NaokiS28/KSystem-573/Extra Hardware/DDR Amp Cage/GN672-PWB(F) - Stereo Power Amplifier/Images/s-l1600-3.jpg

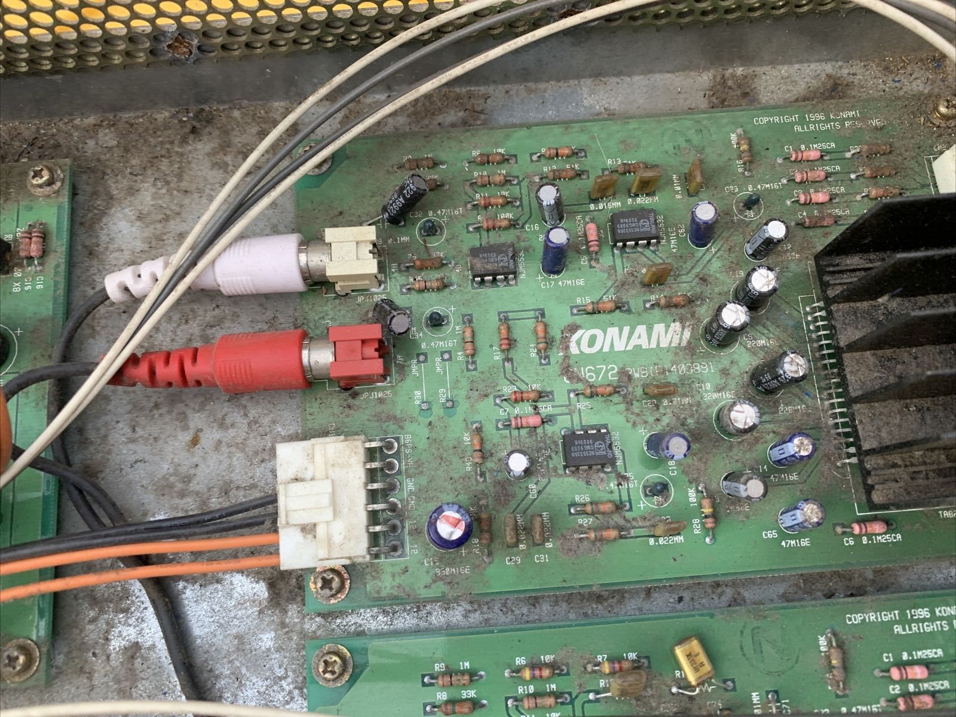
Extra Hardware/DDR Amp Cage/GN672-PWB(F) - Stereo Power Amplifier/Images/s-l1600-3.jpg
