NaokiS28/KSystem-573/Extra Hardware/DDR Amp Cage/GX874-PWB(C) - Stereo pre-amp/images/i-img1200x900-1629526307lxgmrb121866.jpg

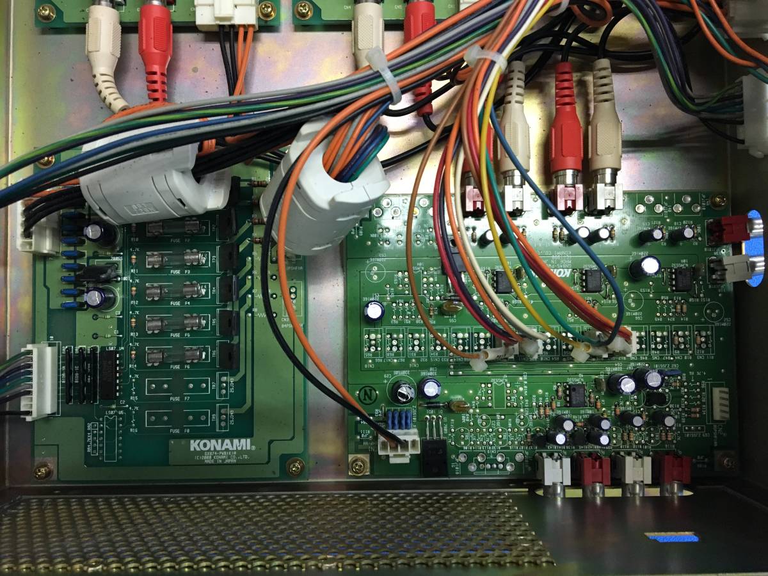
Extra Hardware/DDR Amp Cage/GX874-PWB(C) - Stereo pre-amp/images/i-img1200x900-1629526307lxgmrb121866.jpg
