NaokiS28/KSystem-573/Extra Hardware/DDR Amp Cage/GX874-PWB(C) - Stereo pre-amp/images/s-l1600-4.jpg

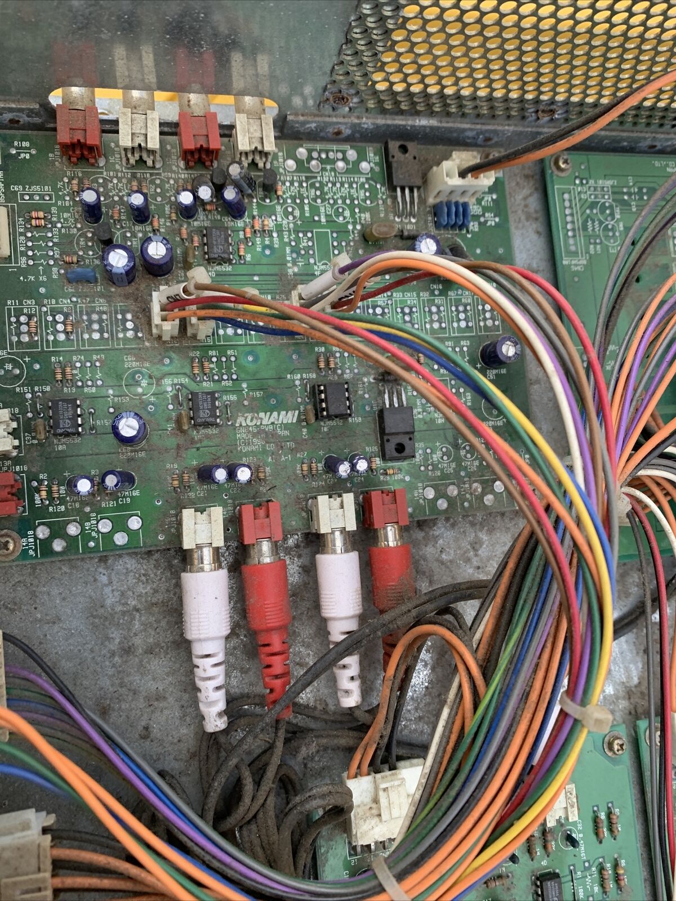
Extra Hardware/DDR Amp Cage/GX874-PWB(C) - Stereo pre-amp/images/s-l1600-4.jpg
