NaokiS28/KSystem-573/Extra Hardware/DDR Amp Cage/Images/IMG_0117.jpg

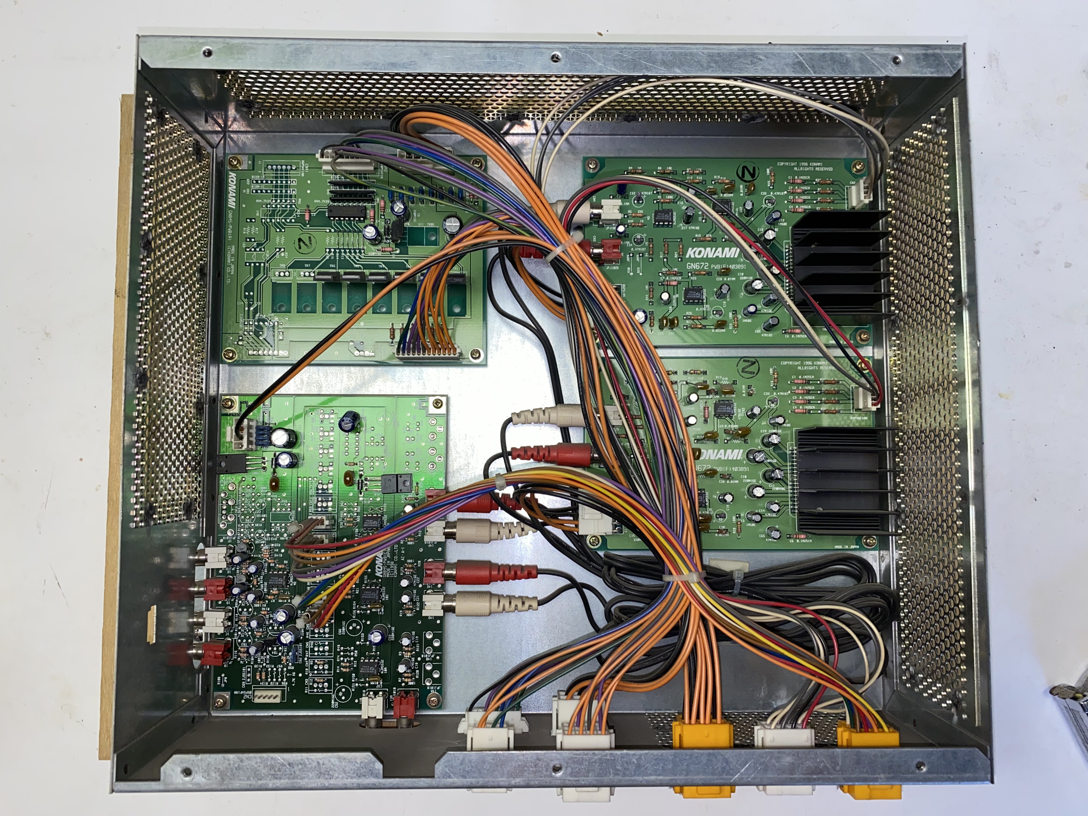
Extra Hardware/DDR Amp Cage/Images/IMG_0117.jpg
