NaokiS28/KSystem-573/Extra Hardware/DDR Amp Cage/Images/s-l1600.jpg

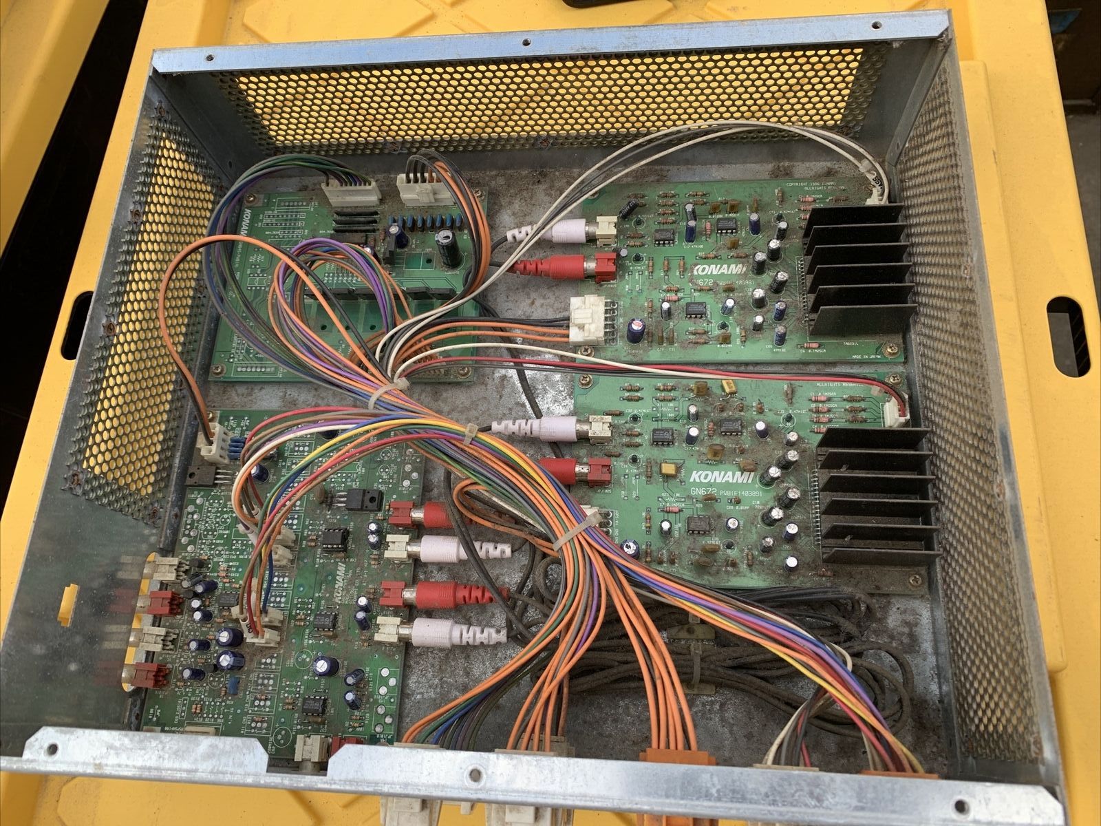
Extra Hardware/DDR Amp Cage/Images/s-l1600.jpg
