NaokiS28/KSystem-573/Extra Hardware/Expansion Boards/GE765-PWB(B)A/E765B1 PAL/E765B1-PAL.png

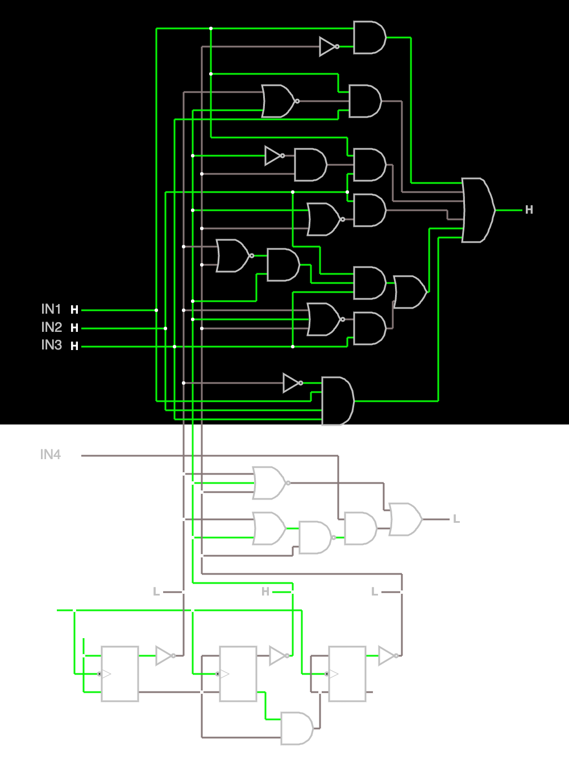
Extra Hardware/Expansion Boards/GE765-PWB(B)A/E765B1 PAL/E765B1-PAL.png
