NaokiS28/KSystem-573/Extra Hardware/Expansion Boards/GunMania IO (PWB0000073070)/Images/s-l1600-1.jpg

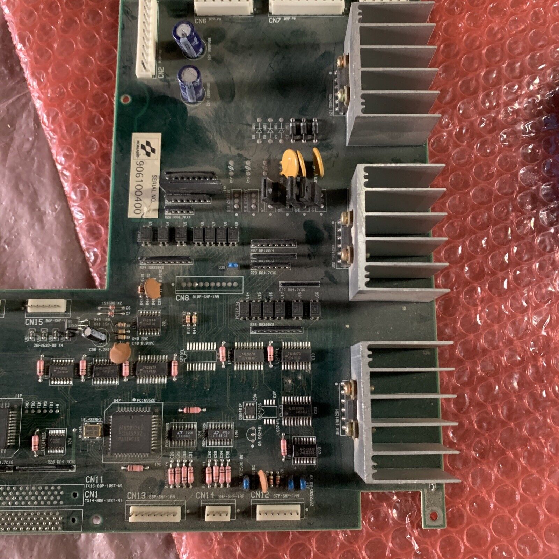
Extra Hardware/Expansion Boards/GunMania IO (PWB0000073070)/Images/s-l1600-1.jpg
