NaokiS28/KSystem-573/Extra Hardware/Expansion Boards/GX700-PWB(F)/images/20220208_194609.jpg

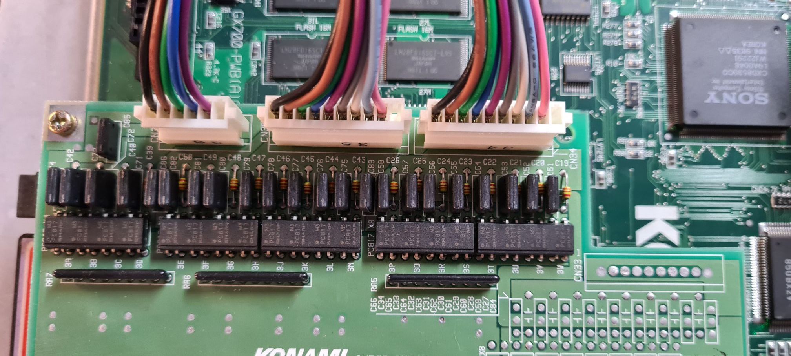
Extra Hardware/Expansion Boards/GX700-PWB(F)/images/20220208_194609.jpg
