NaokiS28/KSystem-573/Extra Hardware/Expansion Boards/GX700-PWB(F)/images/IMG_0334.jpg

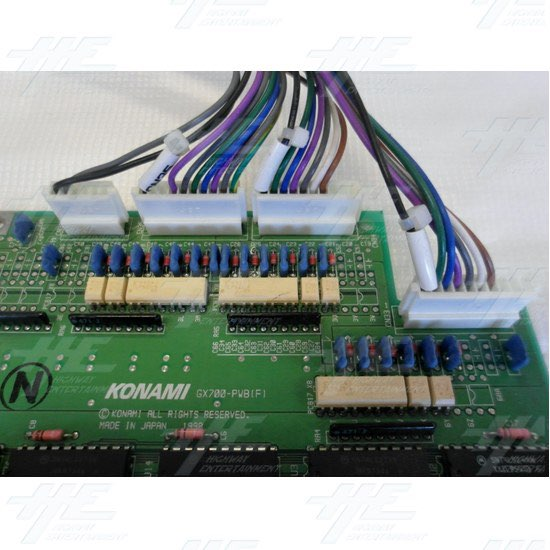
Extra Hardware/Expansion Boards/GX700-PWB(F)/images/IMG_0334.jpg
