NaokiS28/KSystem-573/Extra Hardware/Expansion Boards/GX700-PWB(F)/images/IMG_2689.jpg

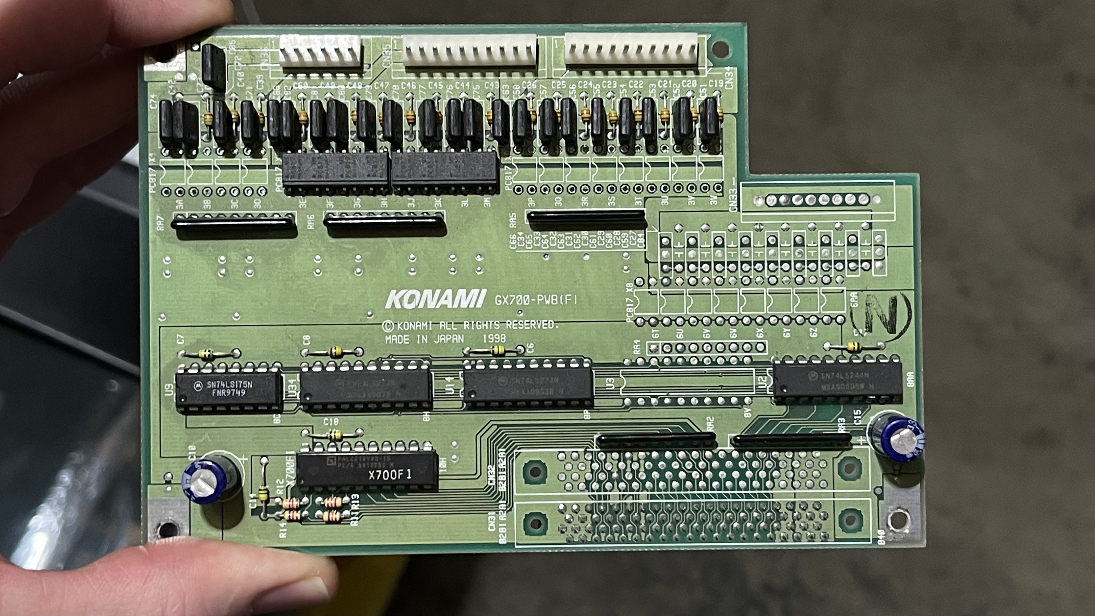
Extra Hardware/Expansion Boards/GX700-PWB(F)/images/IMG_2689.jpg
