NaokiS28/KSystem-573/Extra Hardware/Expansion Boards/GX894-PWB(B)A/Images/IMG_5038.jpeg

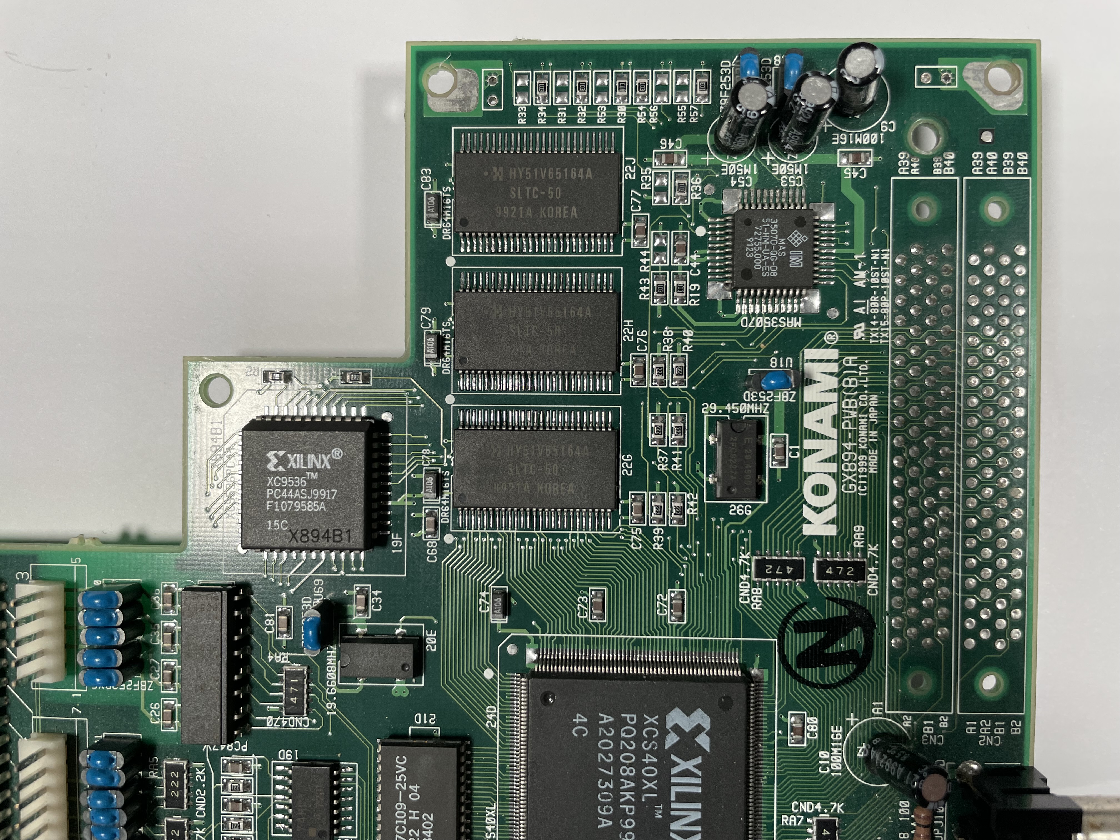
Extra Hardware/Expansion Boards/GX894-PWB(B)A/Images/IMG_5038.jpeg
