NaokiS28/KSystem-573/Extra Hardware/IO Boards/GN845-PWB(B)/Images/20211127_141559.jpg

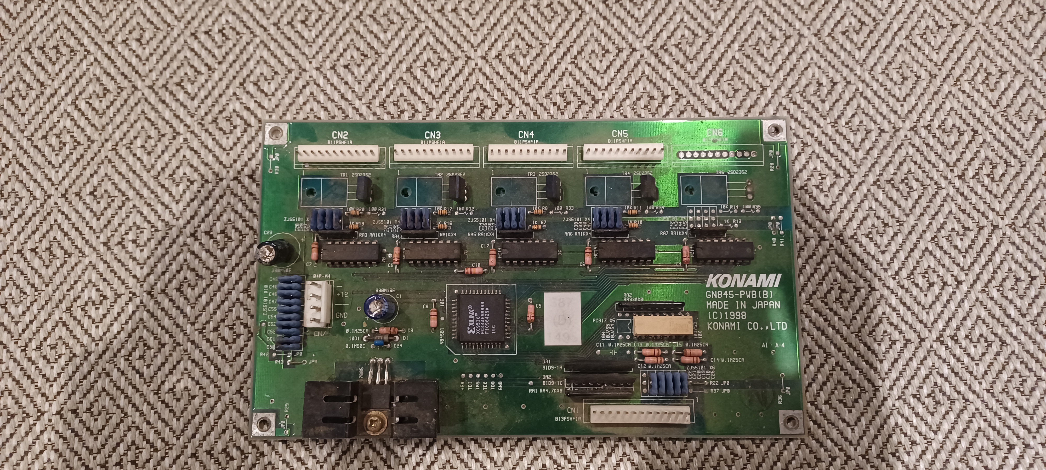
Extra Hardware/IO Boards/GN845-PWB(B)/Images/20211127_141559.jpg
