NaokiS28/KSystem-573/Extra Hardware/IO Boards/GN845-PWB(B)/Images/20211128_125148-1.jpg

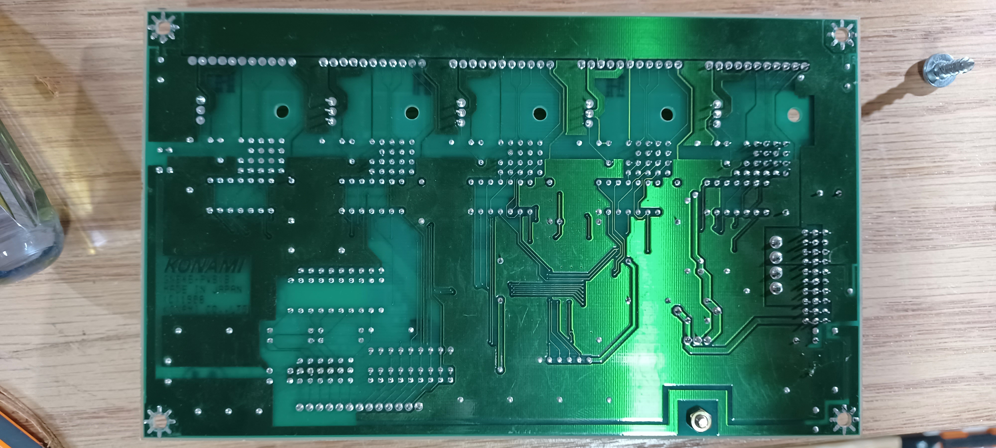
Extra Hardware/IO Boards/GN845-PWB(B)/Images/20211128_125148-1.jpg
