NaokiS28/KSystem-573/Extra Hardware/IO Boards/GN845-PWB(B)/Images/s-l1600-1.jpg

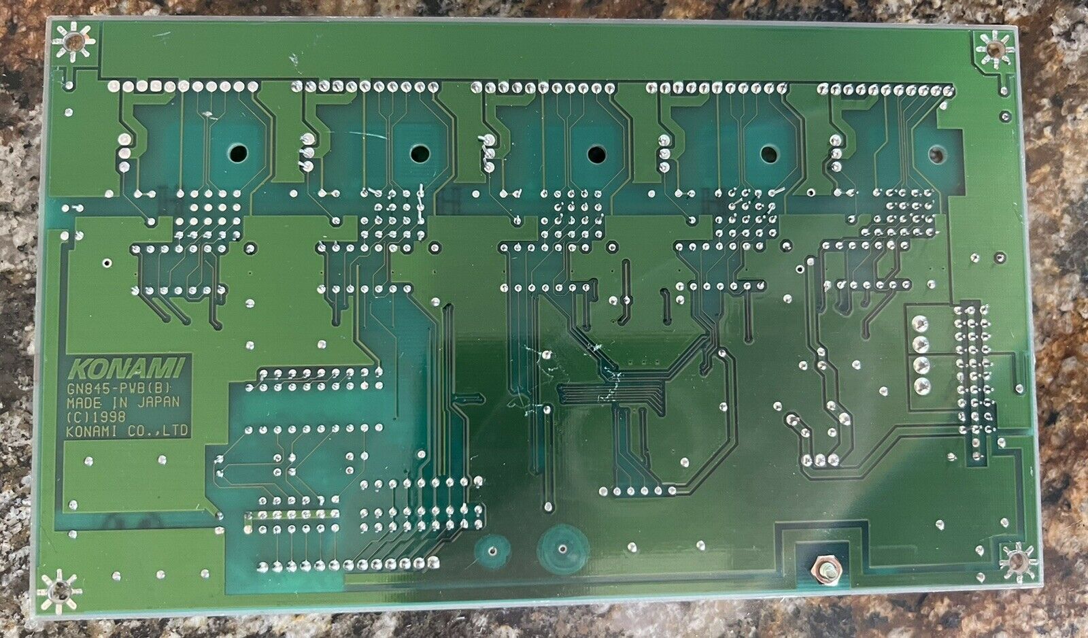
Extra Hardware/IO Boards/GN845-PWB(B)/Images/s-l1600-1.jpg
