NaokiS28/KSystem-573/Extra Hardware/IO Boards/GX874-PWB(K)A/PXL_20221106_212425229-Zoids.jpg

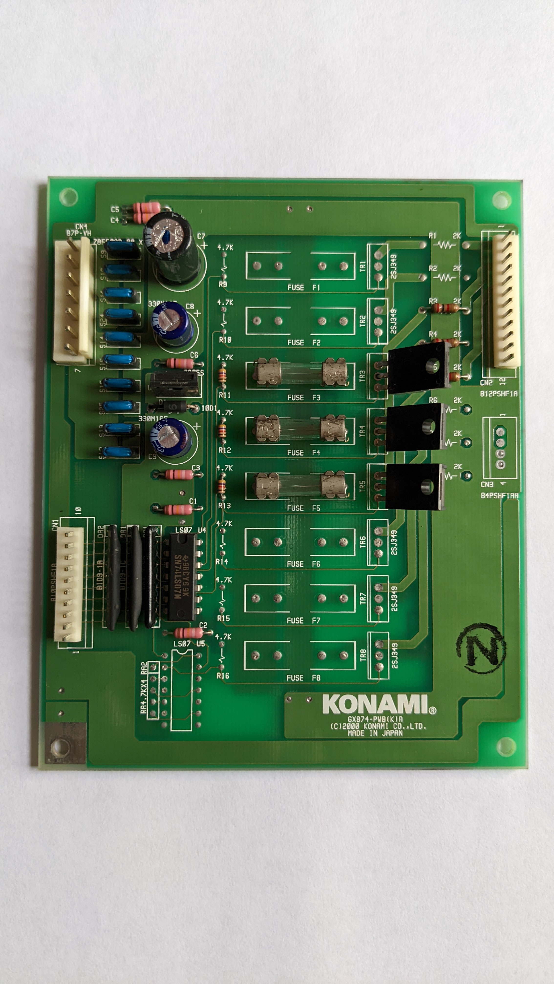
Extra Hardware/IO Boards/GX874-PWB(K)A/PXL_20221106_212425229-Zoids.jpg
