NaokiS28/KSystem-573/Extra Hardware/PCMCIA/PCMCIA extension cable.png

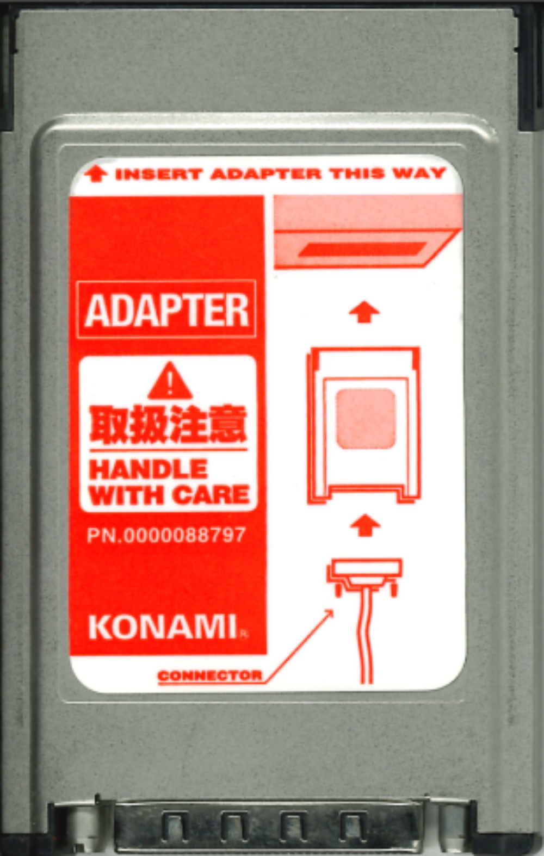
Extra Hardware/PCMCIA/PCMCIA extension cable.png
