NaokiS28/KSystem-573/Extra Hardware/Security Carts/GX700-PWB(J)/Images/IMG_2465.jpg

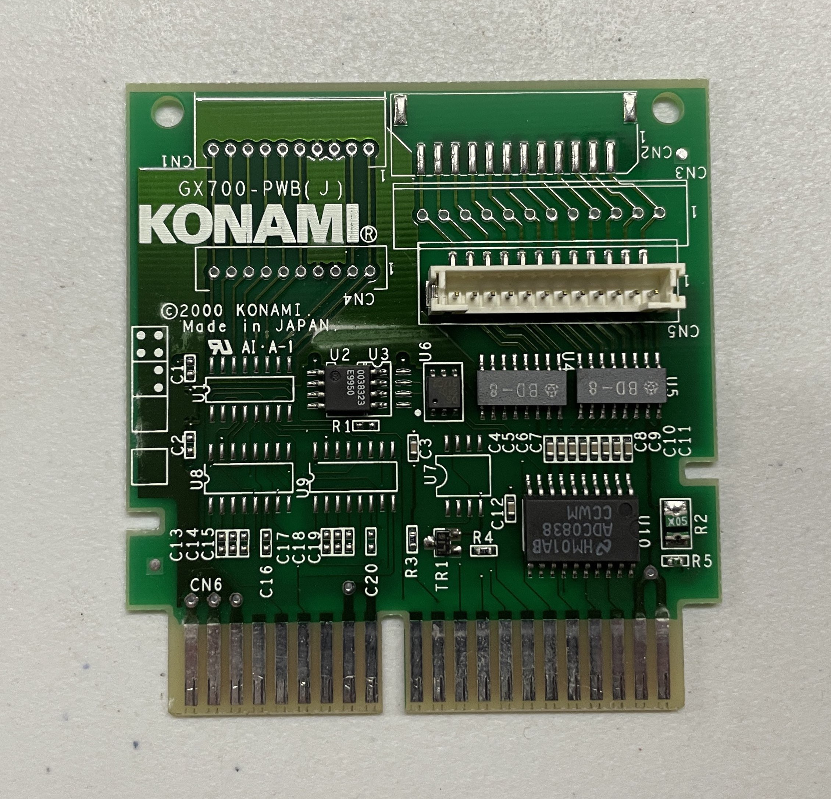
Extra Hardware/Security Carts/GX700-PWB(J)/Images/IMG_2465.jpg
