NaokiS28/KSystem-573/Extra Hardware/Security Carts/GX896-PWB(A)A/Images/IMG_9951.jpg

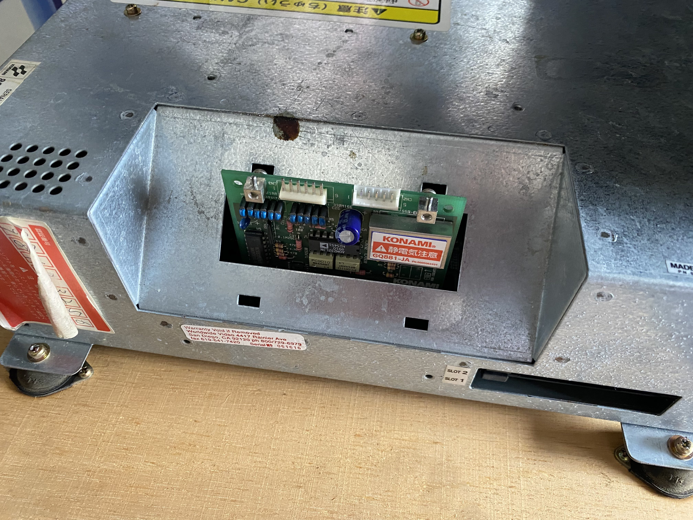
Extra Hardware/Security Carts/GX896-PWB(A)A/Images/IMG_9951.jpg
