NaokiS28/KSystem-573/Images/GX700-PWB(A)C Top.png

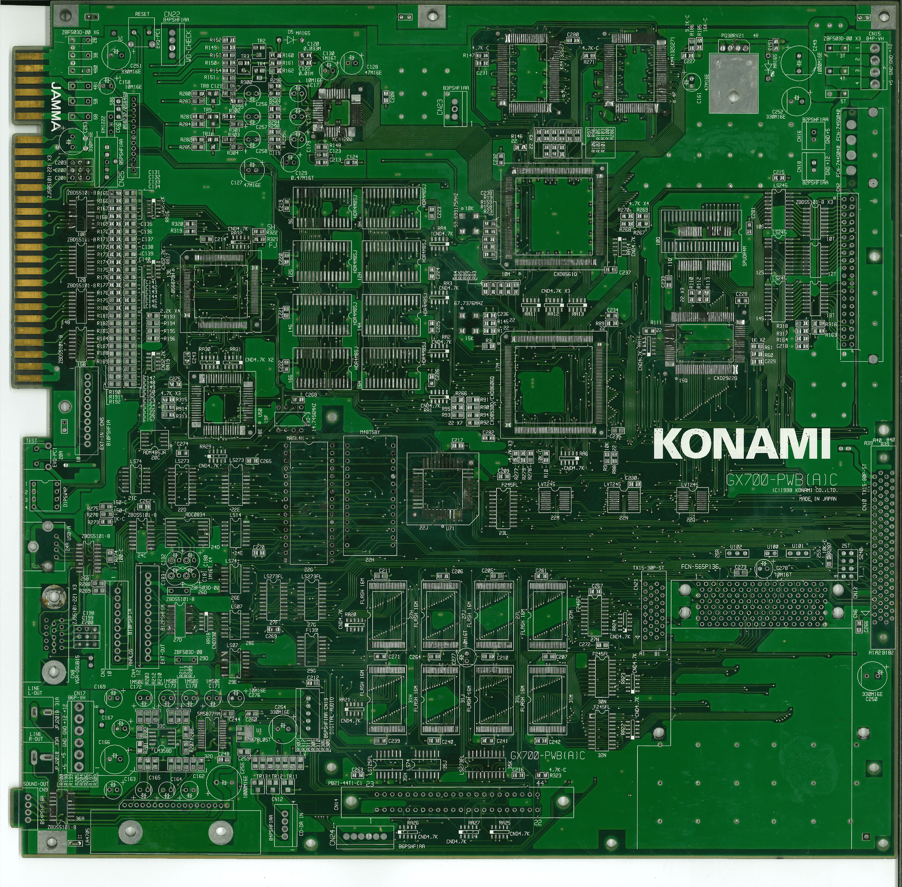
Images/GX700-PWB(A)C Top.png
