NaokiS28/KSystem-573/Images/Rev C/Board Overview.png

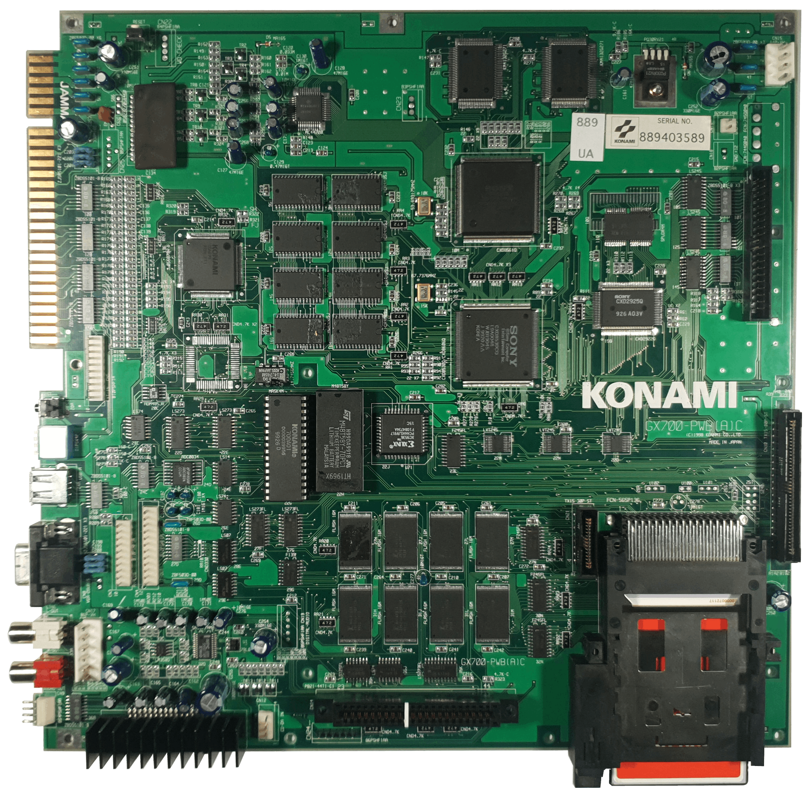
Images/Rev C/Board Overview.png
