NaokiS28/KSystem-573/Images/Watchdog.png

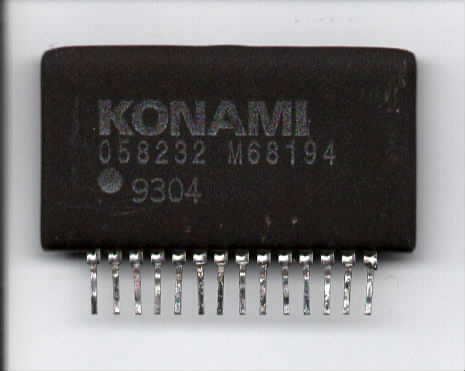
Images/Watchdog.png
