NaokiS28/KSystem-573/Schematics (KiCad)/Konami Flash Card/Images/Back.png

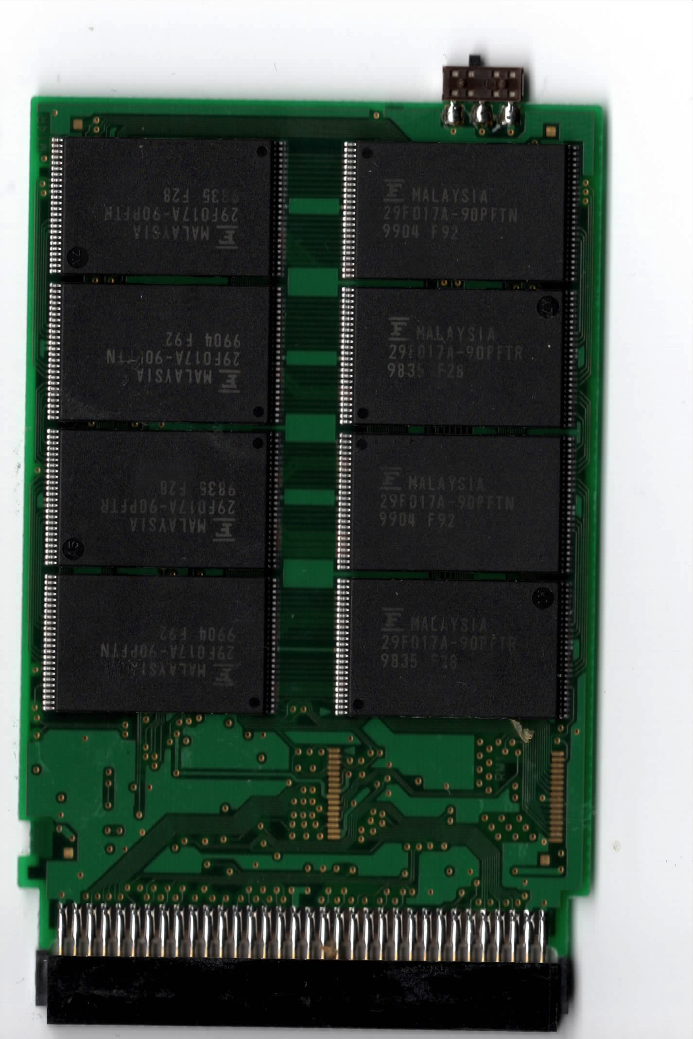
Schematics (KiCad)/Konami Flash Card/Images/Back.png
