NaokiS28/KSystem-573/Schematics (KiCad)/Konami Flash Card/Images/Label-EN.png

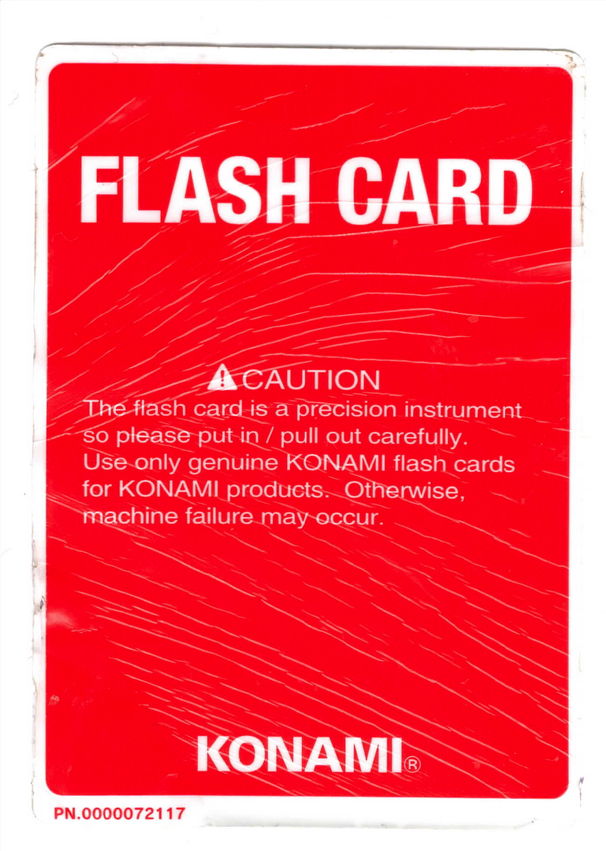
Schematics (KiCad)/Konami Flash Card/Images/Label-EN.png
