NaokiS28/KSystem-573/Extra Hardware/Security Carts/GX896-PWB(A)A/Images/IMG_9953.jpg

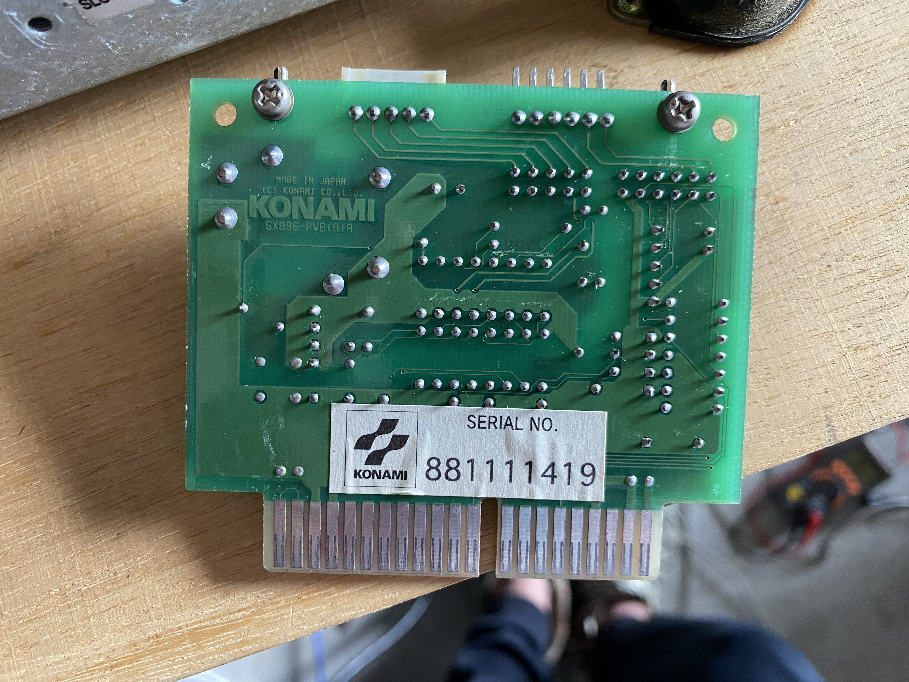
Extra Hardware/Security Carts/GX896-PWB(A)A/Images/IMG_9953.jpg
